Gustbel/S7-PcbDesign/Summits7-Archivos_Fuente_Altium/LibraryUsed/Originales/STEP_Models/INA219_SOT23.STEP

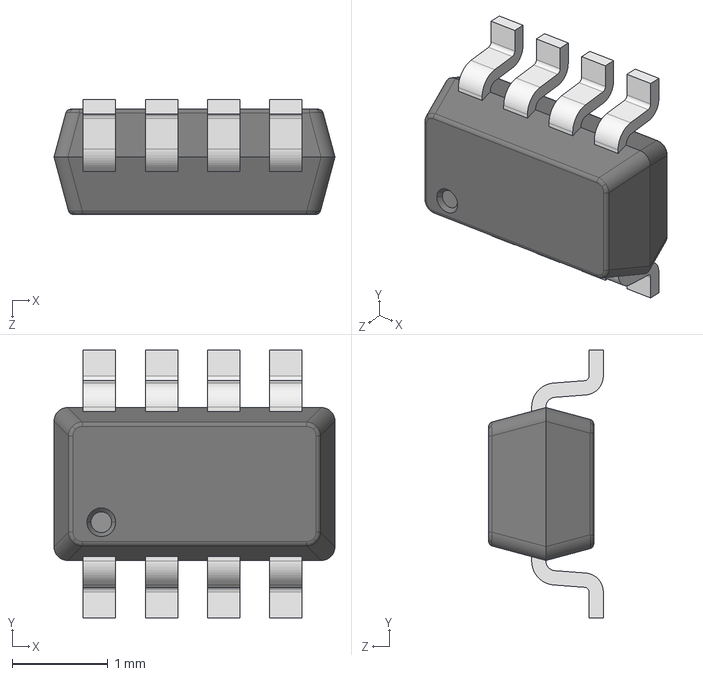
[picture p18: CAD file, 2020-05-08]
Summits7-Archivos_Fuente_Altium/LibraryUsed/Originales/STEP_Models/INA219_SOT23.STEP
2.94 x 2.80 x 1.20 mm
