Gustbel/S7-PcbDesign/Summits7-Archivos_Fuente_Altium/LibraryUsed/Originales/STEP_Models/Header_254mm_Pitch4-1.step

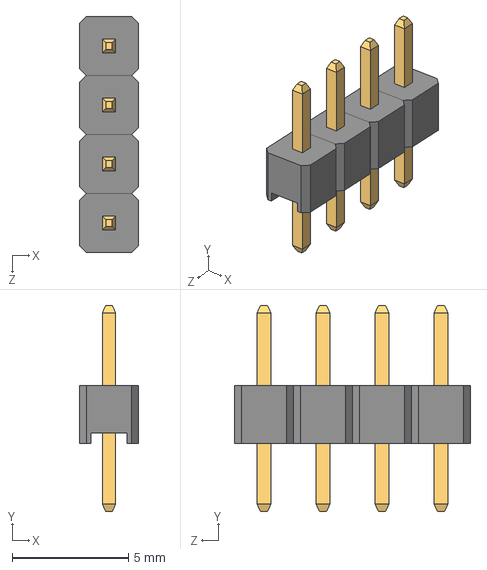
[picture p19: CAD file, 2020-04-10]
Summits7-Archivos_Fuente_Altium/LibraryUsed/Originales/STEP_Models/Header_254mm_Pitch4-1.step
2.54 x 8.88 x 10.2 mm
