Gustbel/S7-PcbDesign/Summits7-Archivos_Fuente_Altium/LibraryUsed/Originales/STEP_Models/Header_254mm_Pitch2-1.step

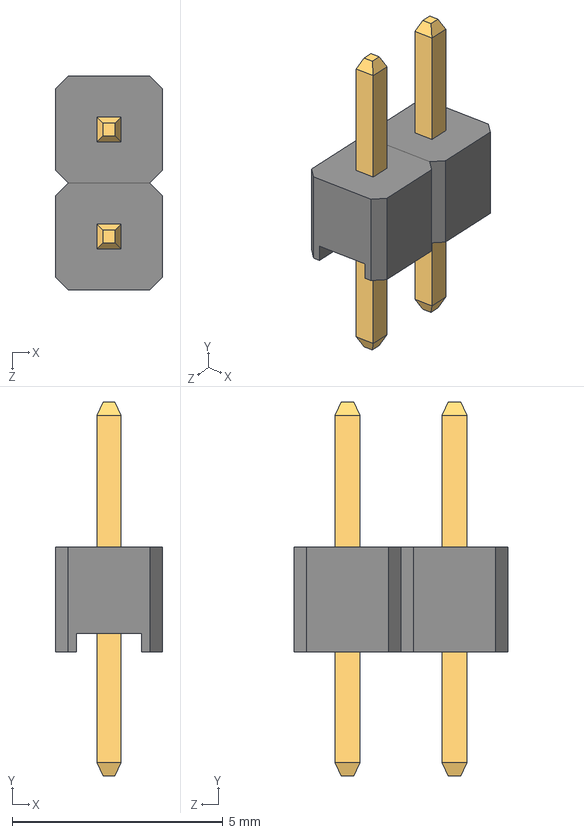
[picture p20: CAD file, 2020-04-08]
Summits7-Archivos_Fuente_Altium/LibraryUsed/Originales/STEP_Models/Header_254mm_Pitch2-1.step
2.54 x 8.88 x 5.08 mm
