Gustbel/S7-PcbDesign/Summits7-Archivos_Fuente_Altium/LibraryUsed/Originales/STEP_Models/PT2512FK-070R1L.STEP

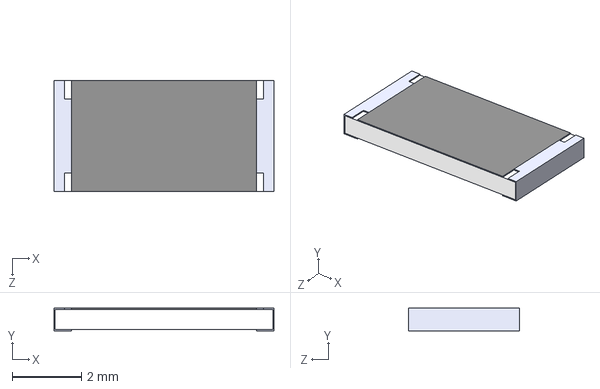
[picture p21: CAD file, 2020-04-08]
Summits7-Archivos_Fuente_Altium/LibraryUsed/Originales/STEP_Models/PT2512FK-070R1L.STEP
6.35 x 0.65 x 3.20 mm
