Gustbel/S7-PcbDesign/Summits7-Archivos_Fuente_Altium/LibraryUsed/Originales/STEP_Models/Res0603.step

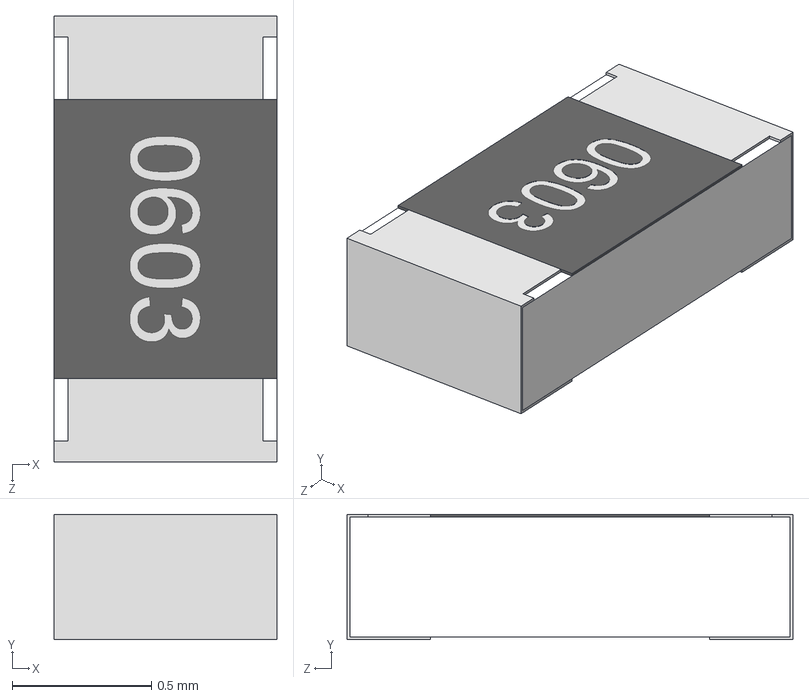
[picture p22: CAD file, 2020-04-07]
Summits7-Archivos_Fuente_Altium/LibraryUsed/Originales/STEP_Models/Res0603.step
0.8 x 0.45 x 1.60 mm
