Gustbel/S7-PcbDesign/Summits7-Archivos_Fuente_Altium/LibraryUsed/Originales/STEP_Models/Cap1210.step

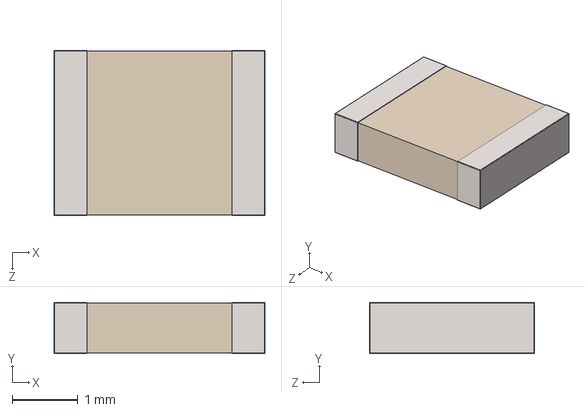
[picture p23: CAD file, 2020-04-07]
Summits7-Archivos_Fuente_Altium/LibraryUsed/Originales/STEP_Models/Cap1210.step
3.20 x 0.78 x 2.50 mm
