Gustbel/S7-PcbDesign/Summits7-Archivos_Fuente_Altium/LibraryUsed/Originales/STEP_Models/Cap0603.step

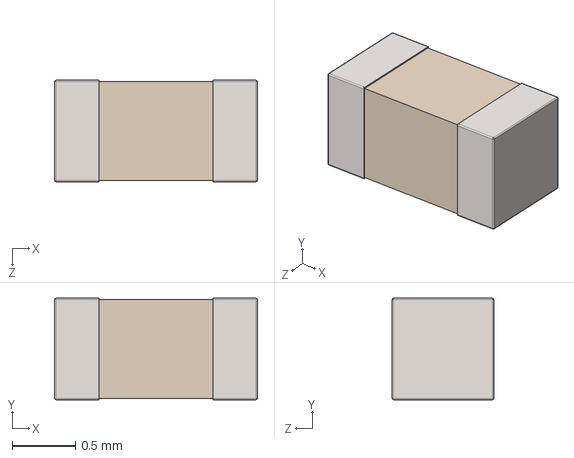
[picture p24: CAD file, 2020-04-07]
Summits7-Archivos_Fuente_Altium/LibraryUsed/Originales/STEP_Models/Cap0603.step
1.60 x 0.8 x 0.8 mm
