Gustbel/S7-PcbDesign/Summits7-Archivos_Fuente_Altium/LibraryUsed/Originales/STEP_Models/Fotodiodo_VBPW34S.step

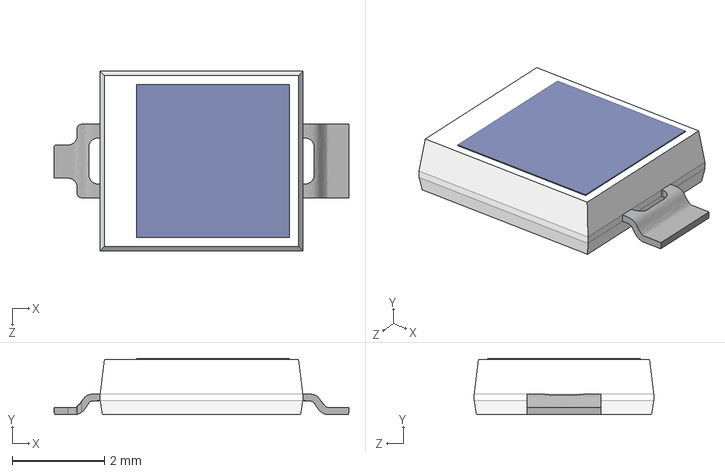
[picture p25: CAD file, 2020-04-07]
Summits7-Archivos_Fuente_Altium/LibraryUsed/Originales/STEP_Models/Fotodiodo_VBPW34S.step
6.41 x 1.22 x 3.90 mm
