Gustbel/S7-PcbDesign/Summits7-Archivos_Fuente_Altium/LibraryUsed/Originales/STEP_Models/LED_HSMW-C191.STEP

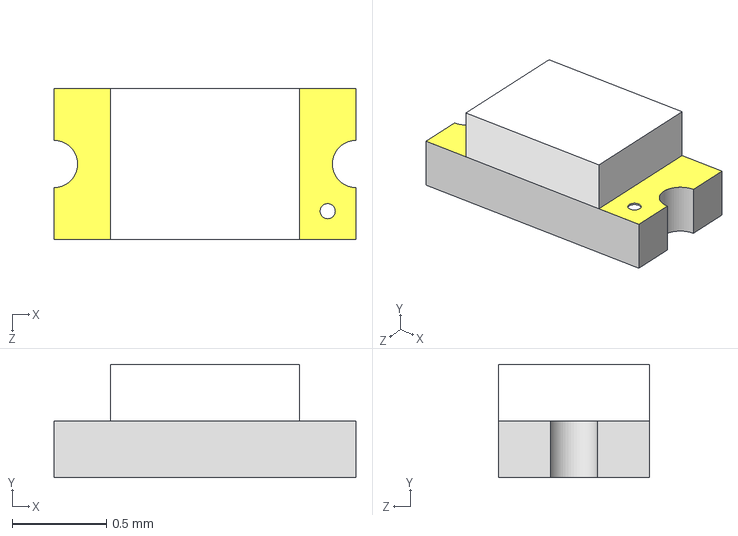
[picture p26: CAD file, 2020-04-07]
Summits7-Archivos_Fuente_Altium/LibraryUsed/Originales/STEP_Models/LED_HSMW-C191.STEP
1.60 x 0.6 x 0.8 mm
