Gustbel/S7-PcbDesign/Summits7-Archivos_Fuente_Altium/LibraryUsed/Originales/STEP_Models/SS34_DO214AB.step

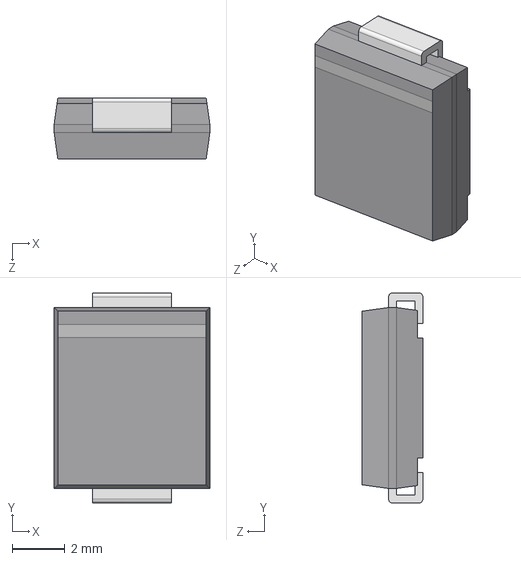
[picture p27: CAD file, 2020-04-07]
Summits7-Archivos_Fuente_Altium/LibraryUsed/Originales/STEP_Models/SS34_DO214AB.step
5.90 x 7.95 x 2.30 mm
