Gustbel/S7-PcbDesign/Summits7-Archivos_Fuente_Altium/LibraryUsed/Originales/STEP_Models/ABM8-26MHz.STEP

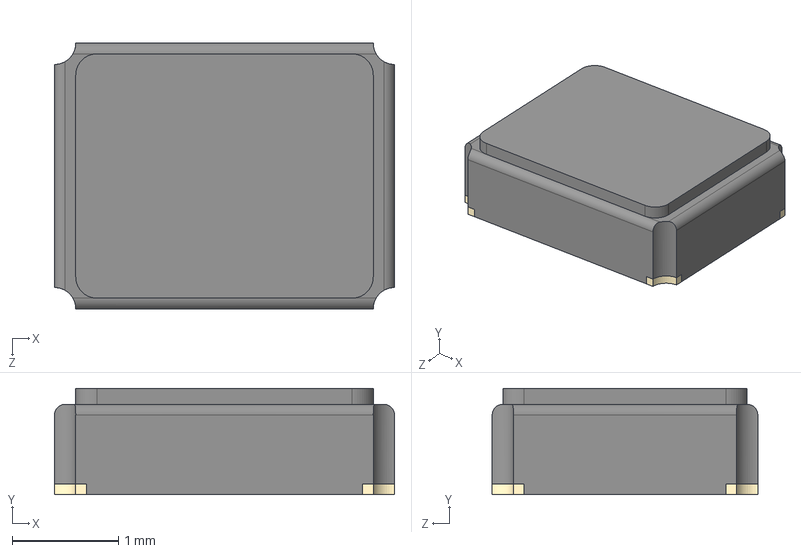
[picture p28: CAD file, 2020-04-07]
Summits7-Archivos_Fuente_Altium/LibraryUsed/Originales/STEP_Models/ABM8-26MHz.STEP
3.20 x 1.00 x 2.50 mm
