Gustbel/S7-PcbDesign/Summits7-Archivos_Fuente_Altium/LibraryUsed/Originales/STEP_Models/LT1171ST-3V3_SOT223.STEP

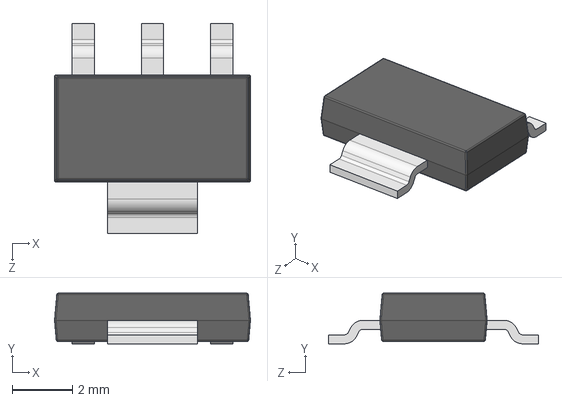
[picture p29: CAD file, 2020-04-06]
Summits7-Archivos_Fuente_Altium/LibraryUsed/Originales/STEP_Models/LT1171ST-3V3_SOT223.STEP
6.50 x 1.68 x 6.96 mm
