Gustbel/S7-PcbDesign/Summits7-Archivos_Fuente_Altium/LibraryUsed/Originales/STEP_Models/ESP8266EX.STEP

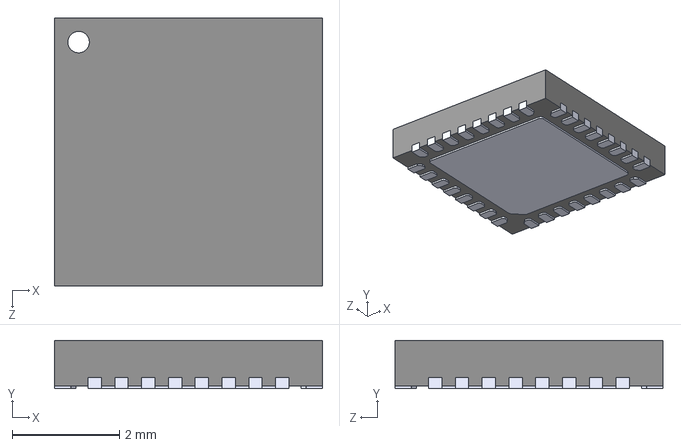
[picture p30: CAD file, 2020-04-06]
Summits7-Archivos_Fuente_Altium/LibraryUsed/Originales/STEP_Models/ESP8266EX.STEP
5.00 x 0.9 x 5.00 mm
