Gustbel/S7-PcbDesign/Summits7-Archivos_Fuente_Altium/LibraryUsed/Originales/STEP_Models/Tl072CD_SOIC127P600X175-8N.step

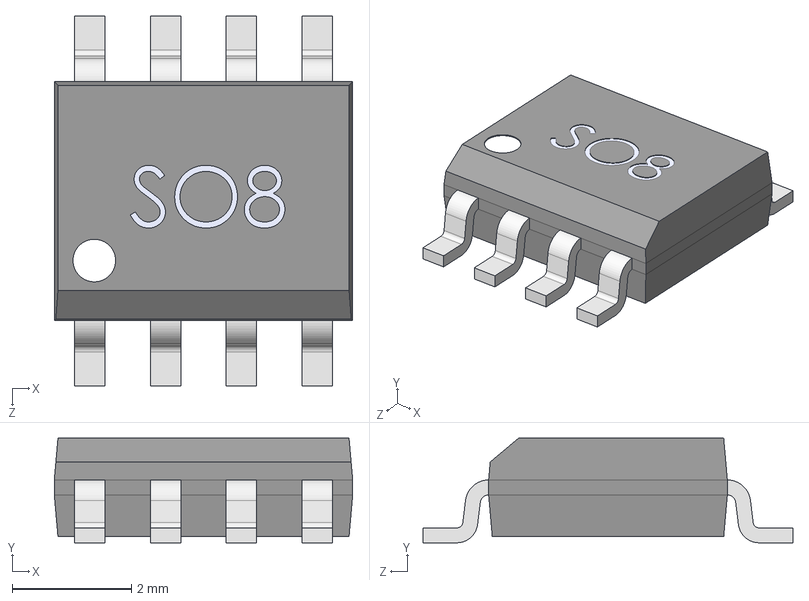
[picture p31: CAD file, 2020-04-06]
Summits7-Archivos_Fuente_Altium/LibraryUsed/Originales/STEP_Models/Tl072CD_SOIC127P600X175-8N.step
5.00 x 1.75 x 6.20 mm
