Gustbel/S7-PcbDesign/Summits7-Archivos_Fuente_Altium/LibraryUsed/Originales/STEP_Models/MP1584_SOIC127P600X170-9N.step

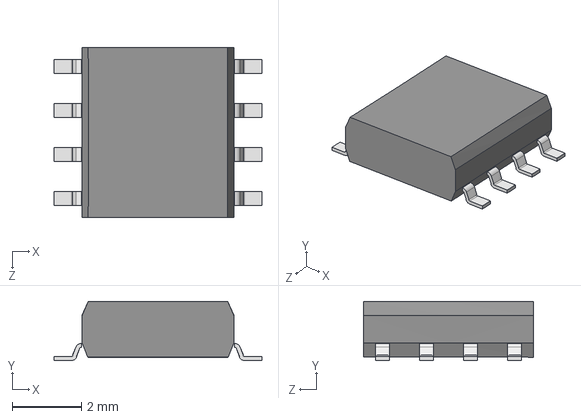
[picture p32: CAD file, 2020-04-06]
Summits7-Archivos_Fuente_Altium/LibraryUsed/Originales/STEP_Models/MP1584_SOIC127P600X170-9N.step
6.00 x 1.71 x 4.90 mm
